JarekParal/FI-MUNI_People-counter-board/pcb_eagle/people-counter-74xx.sch

## EAGLE design pcb_eagle/people-counter-74xx.sch (2018-09-18, an earlier design)

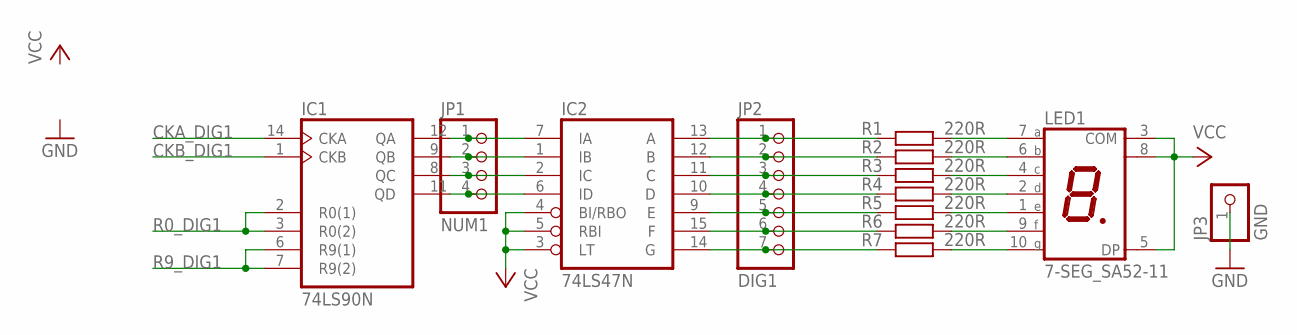
[picture p6: schematic people-counter-74xx.sch]

Parts:
IC1: 74LS90N; DIL14
IC2: 74LS47N; DIL16
JP1: NUM1; 1X04
JP2: DIG1; 1X07
JP3: GND; 1X01
LED1: 7-SEG_SA52-11; SA52-11
R1, R2, R3, R4, R5, R6, R7: 220R; R0603

Connections:
A_DIG1: IC2.13 (A), JP2.1, R1.1
A_DIG_1: LED1.7 (A), R1.2
B_DIG1: IC2.12 (B), JP2.2, R2.1
B_DIG_1: LED1.6 (B), R2.2
CKA_DIG1: IC1.14 (CKA)
CKB_DIG1: IC1.1 (CKB)
C_DIG1: IC2.11 (C), JP2.3, R3.1
C_DIG_1: LED1.4 (C), R3.2
D_DIG1: IC2.10 (D), JP2.4, R4.1
D_DIG_1: LED1.2 (D), R4.2
E_DIG1: IC2.9 (E), JP2.5, R5.1
E_DIG_1: LED1.1 (E), R5.2
F_DIG1: IC2.15 (F), JP2.6, R6.1
F_DIG_1: LED1.9 (F), R6.2
GND: JP3.1
G_DIG1: IC2.14 (G), JP2.7, R7.1
G_DIG_1: LED1.10 (G), R7.2
QA_IA_DIG1: IC1.12 (QA), IC2.7 (IA), JP1.1
QB_IB_DIG1: IC1.9 (QB), IC2.1 (IB), JP1.2
QC_IC_DIG1: IC1.8 (QC), IC2.2 (IC), JP1.3
QD_ID_DIG1: IC1.11 (QD), IC2.6 (ID), JP1.4
R0_DIG1: IC1.2 (R0(1)), IC1.3 (R0(2))
R9_DIG1: IC1.6 (R9(1)), IC1.7 (R9(2))
VCC: IC2.3 (LT), IC2.4 (BI/RBO), IC2.5 (RBI), LED1.3 (COM), LED1.5 (DP), LED1.8 (COM)
